tasifkhan/project_thermistor/desktop_app/data/2017_09_13_18_55_16_1_temp_25.png

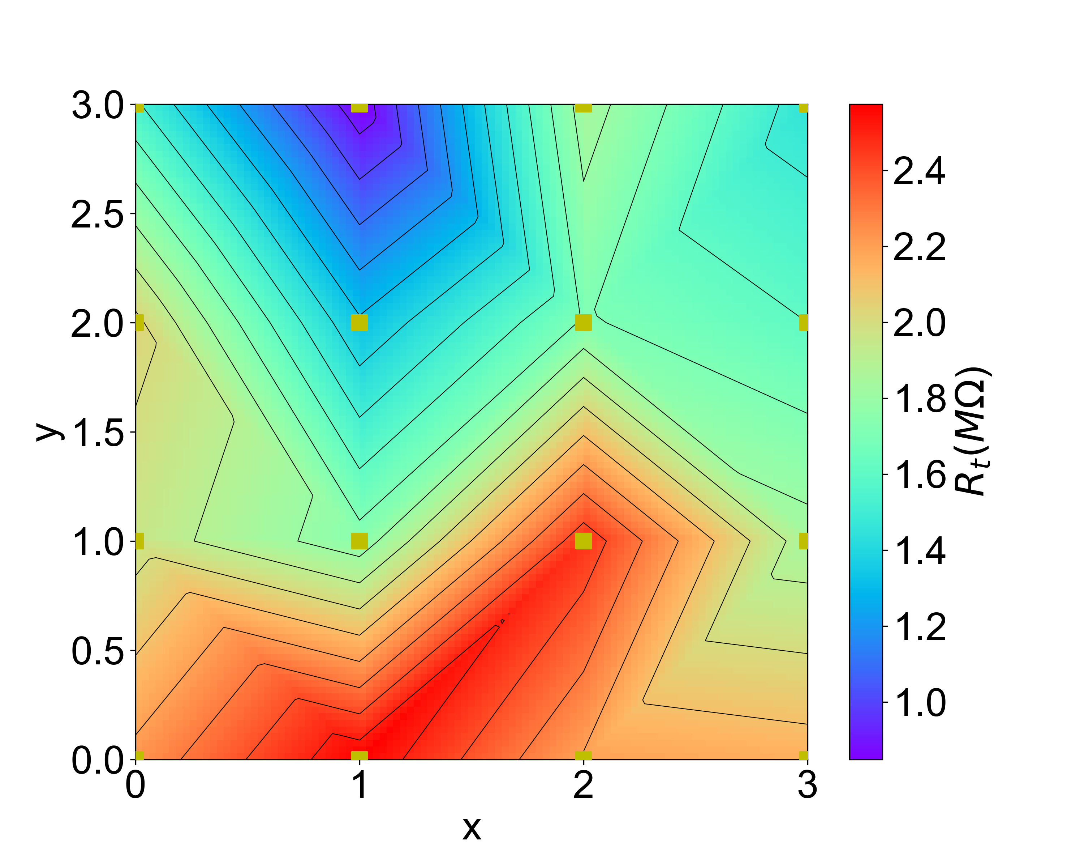
desktop_app/data/2017_09_13_18_55_16_1_temp_25.png
