tasifkhan/project_thermistor/desktop_app/data/2017_09_12_encapsulated thermistor_stencil/2017_09_12_encapsulated thermistor_stencil_plot_full.png

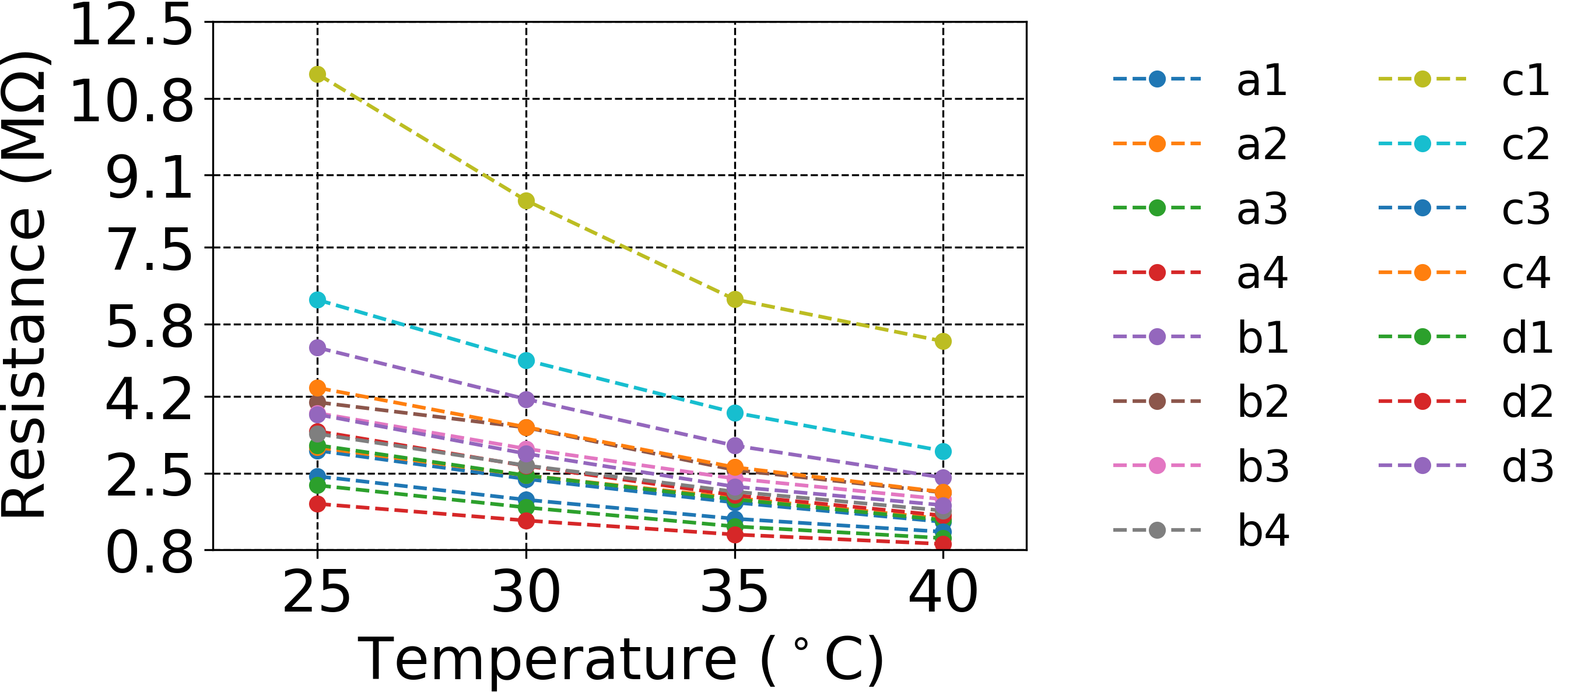
desktop_app/data/2017_09_12_encapsulated thermistor_stencil/2017_09_12_encapsulated thermistor_stencil_plot_full.png
