tasifkhan/project_thermistor/desktop_app/data/2017_09_13_18_42_19_1_calculated_temp_fing.png

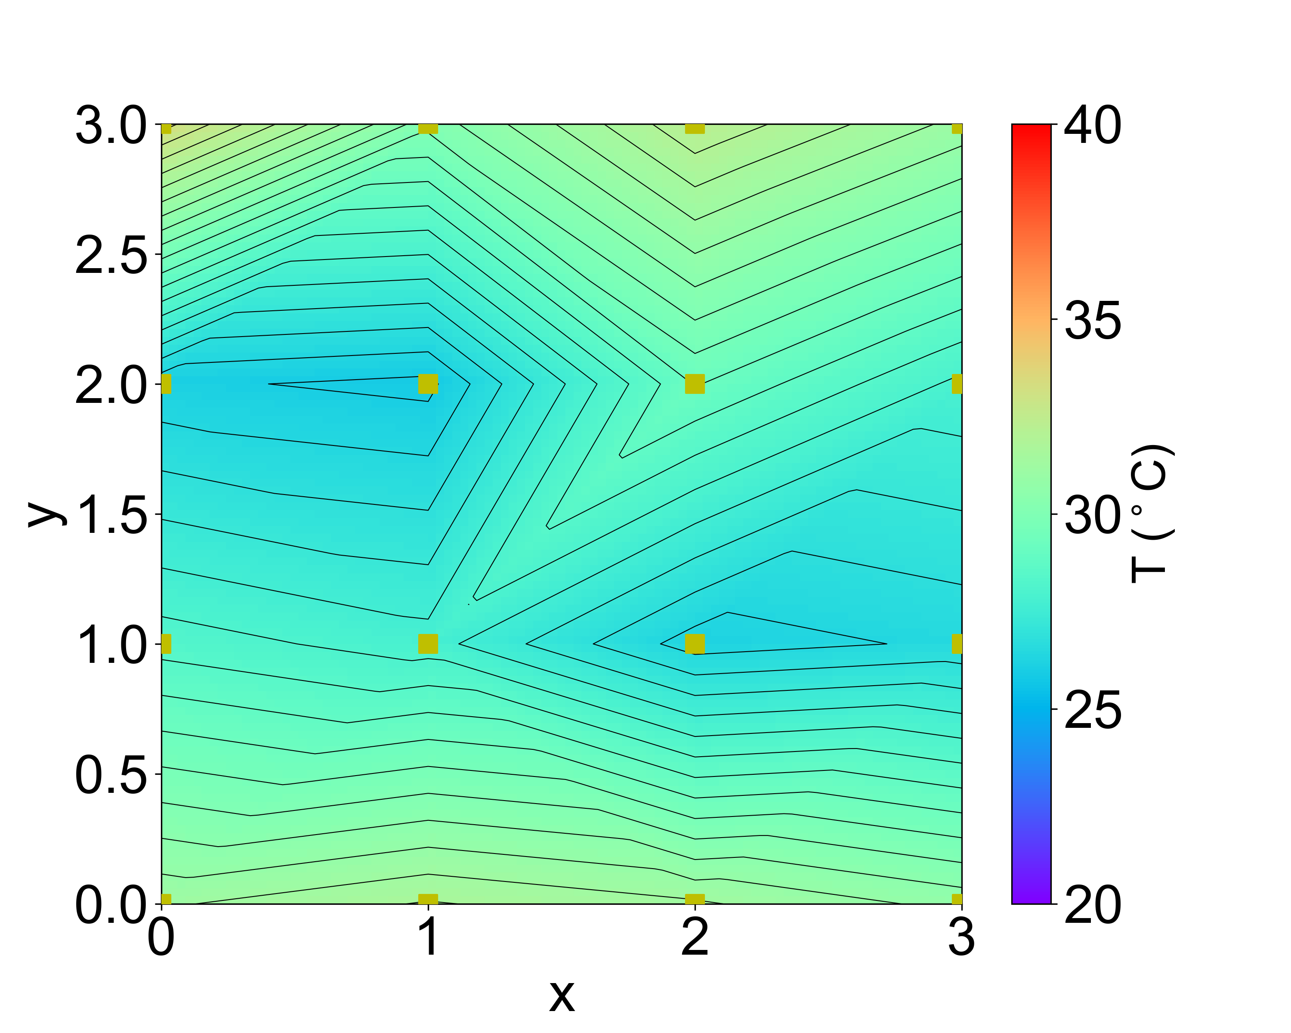
desktop_app/data/2017_09_13_18_42_19_1_calculated_temp_fing.png
