tasifkhan/project_thermistor/desktop_app/data/2017_09_13_18_56_21_1_beta_plot.png

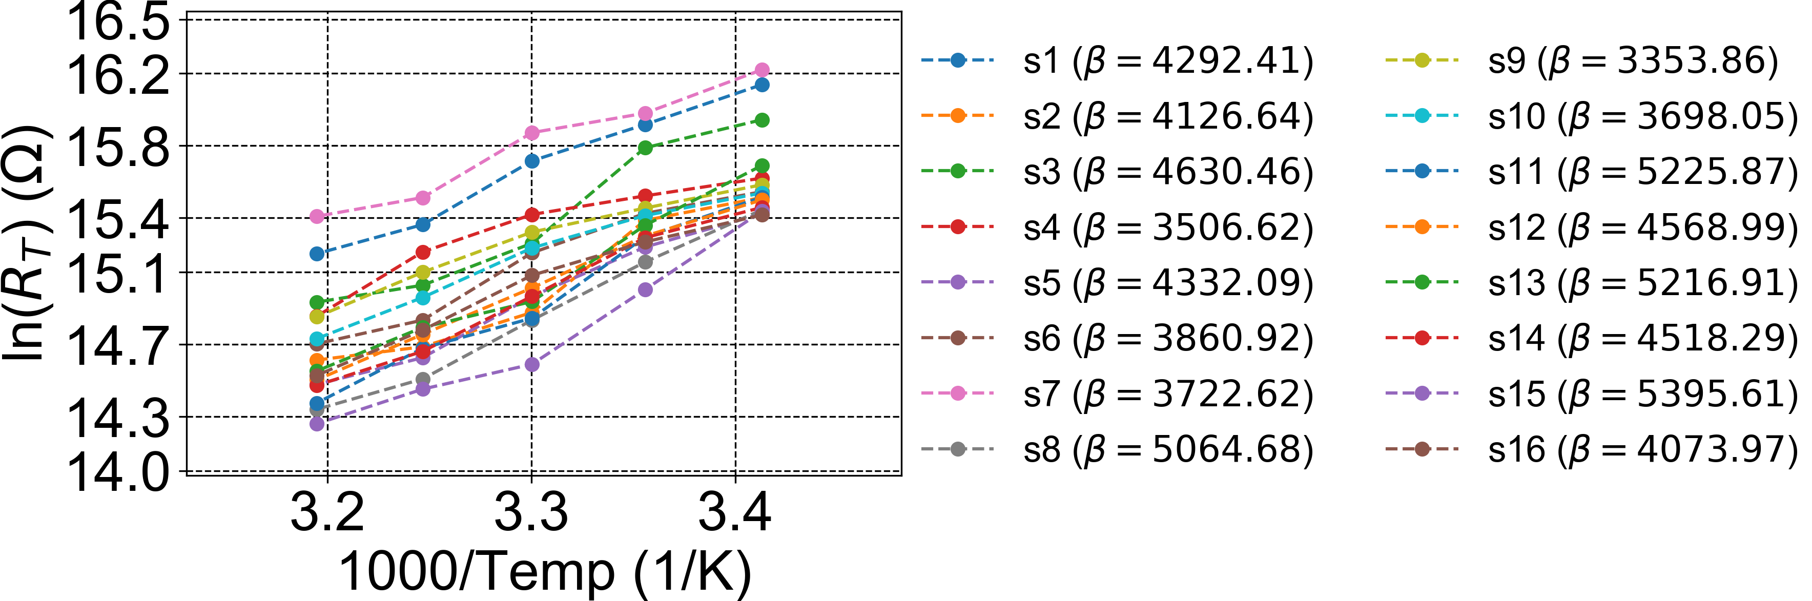
desktop_app/data/2017_09_13_18_56_21_1_beta_plot.png
