tasifkhan/project_thermistor/desktop_app/data/2017_09_13_18_57_37_1_calculated_temp_f.png

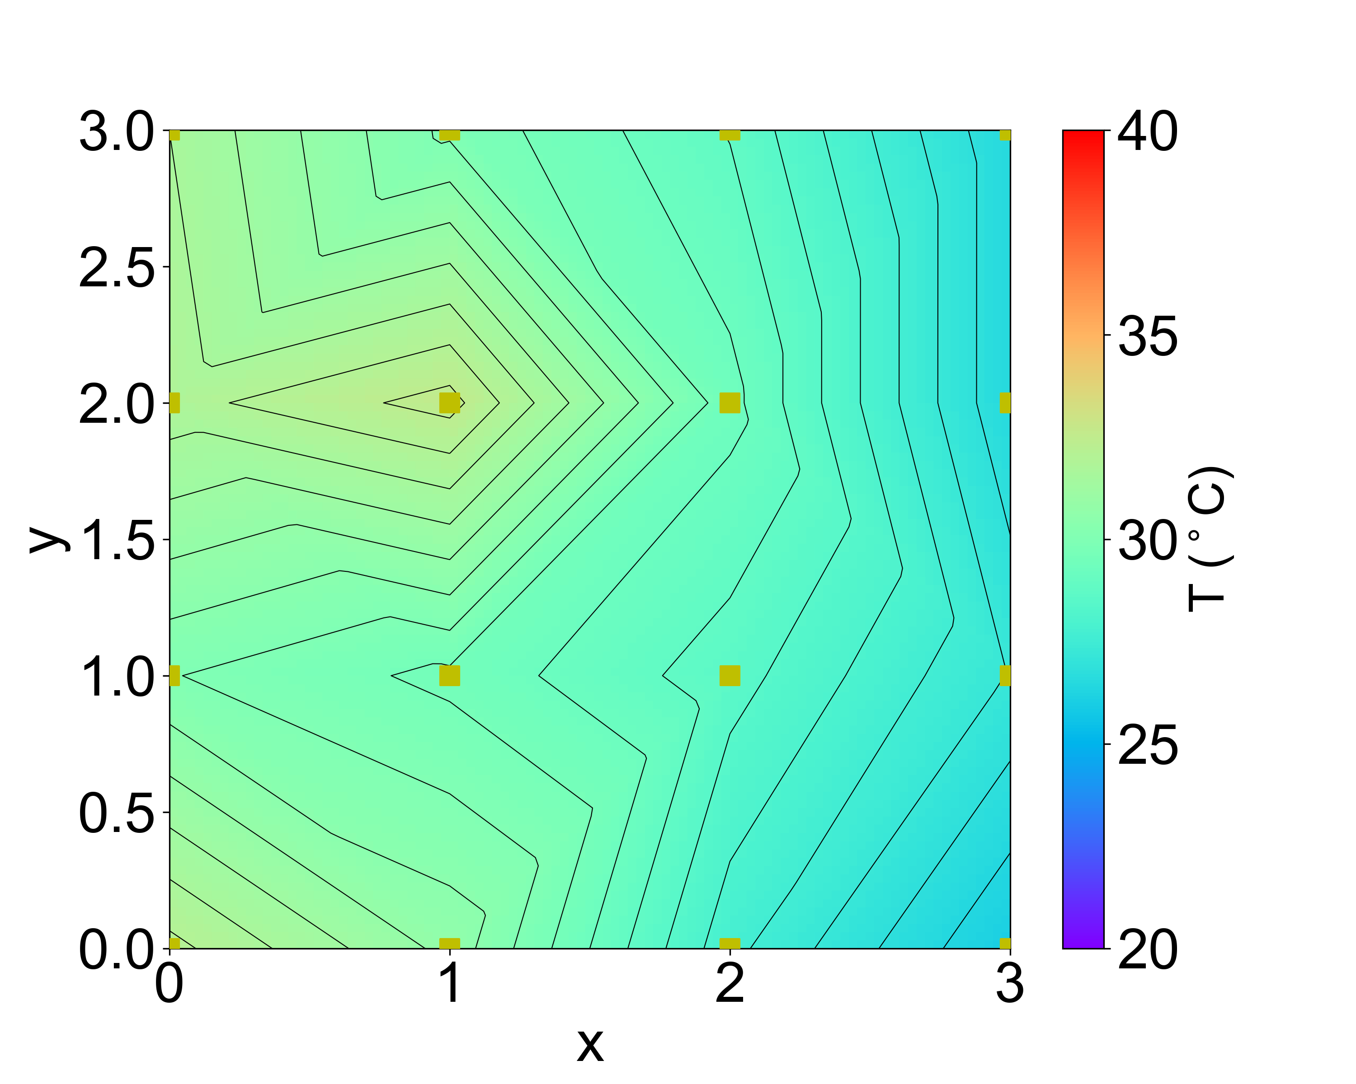
desktop_app/data/2017_09_13_18_57_37_1_calculated_temp_f.png
