tasifkhan/project_thermistor/desktop_app/data/_template_beta_plot.png

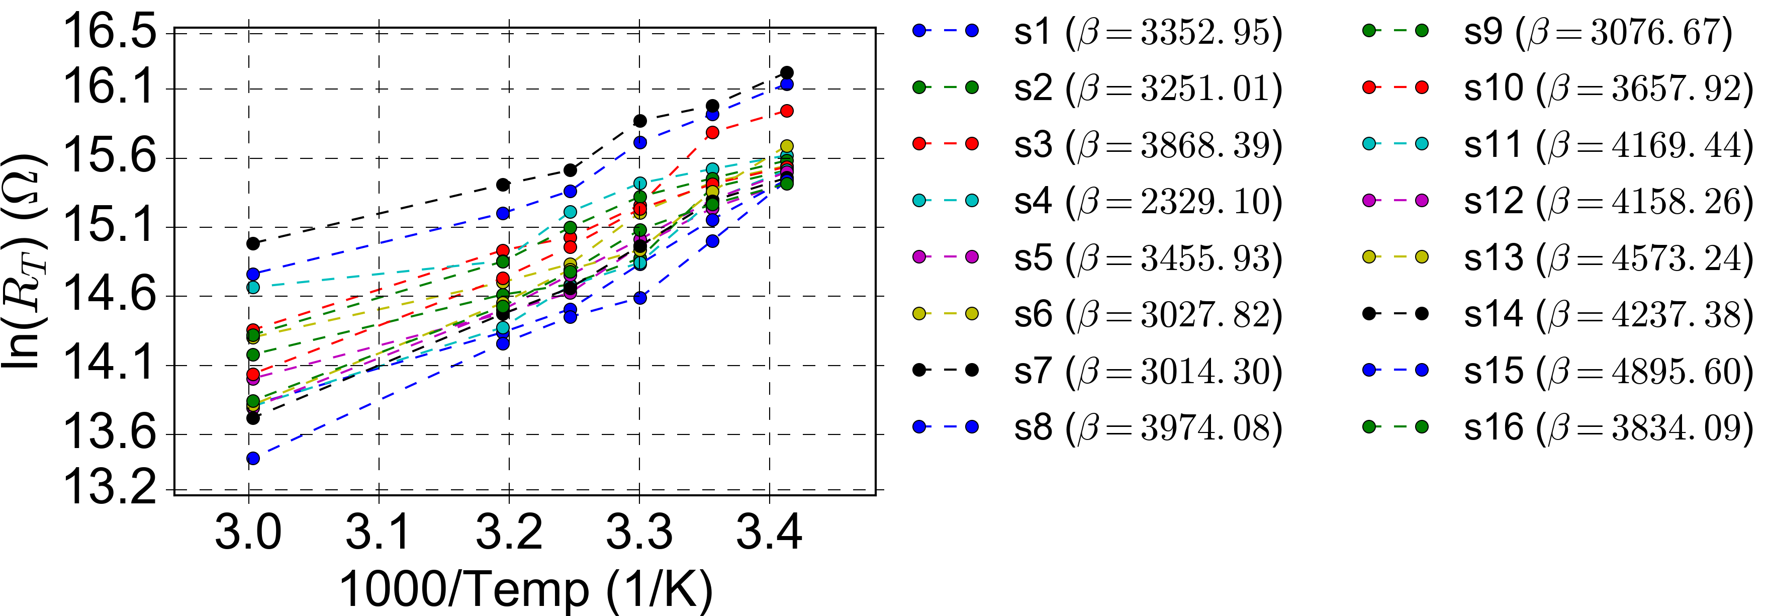
desktop_app/data/_template_beta_plot.png
